maarten-pennings/P2000-cartridge/case/label-ErixCollectables-black.png

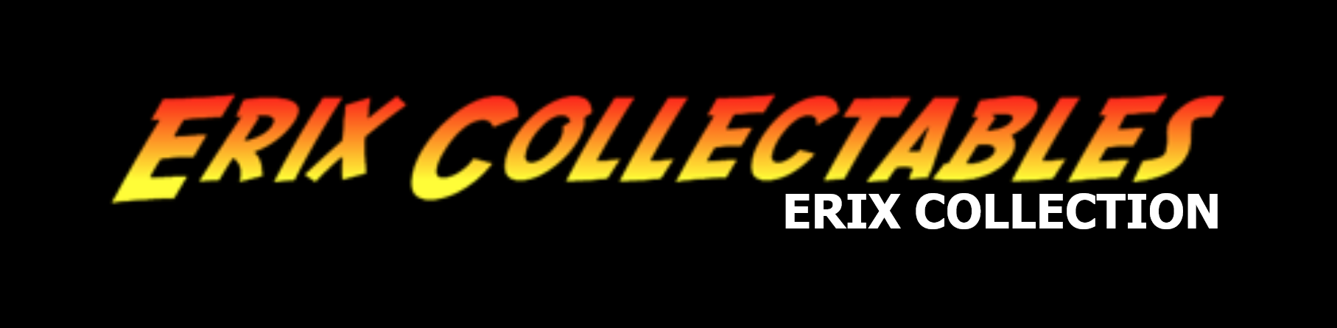
case/label-ErixCollectables-black.png
