maarten-pennings/P2000-cartridge/case/label-ErixCollectables-white.png

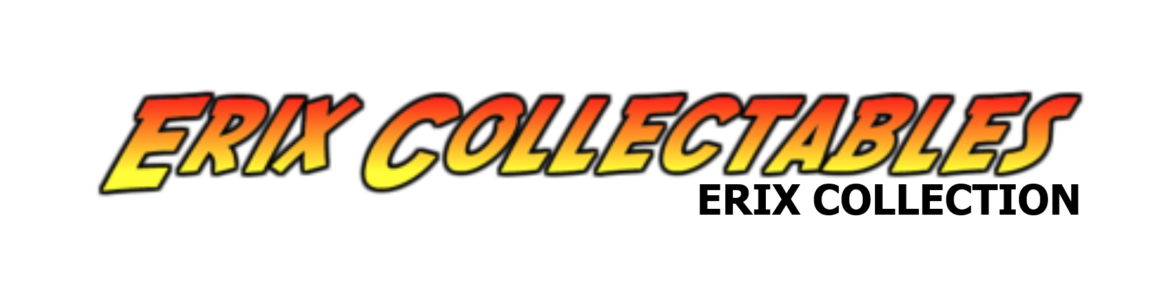
case/label-ErixCollectables-white.png
