maarten-pennings/P2000-cartridge/images/cartridge.jpg

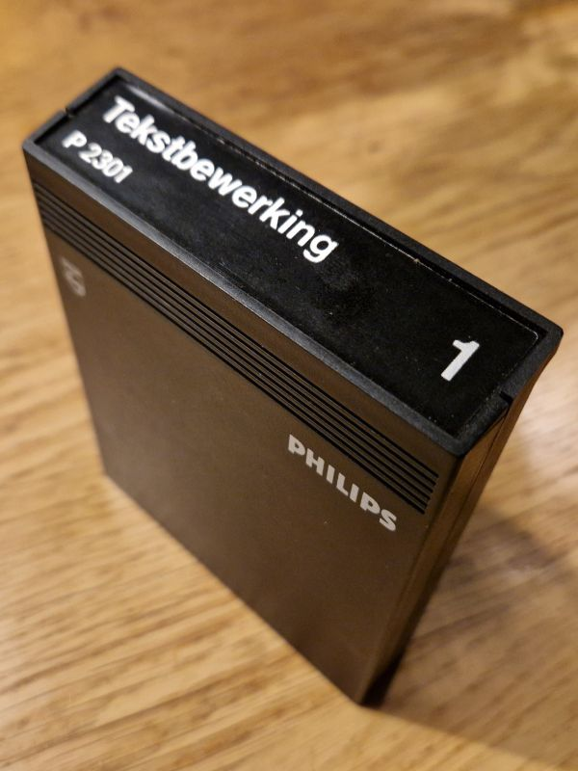
images/cartridge.jpg
