maarten-pennings/P2000-cartridge/images/invoice3Dprint.png

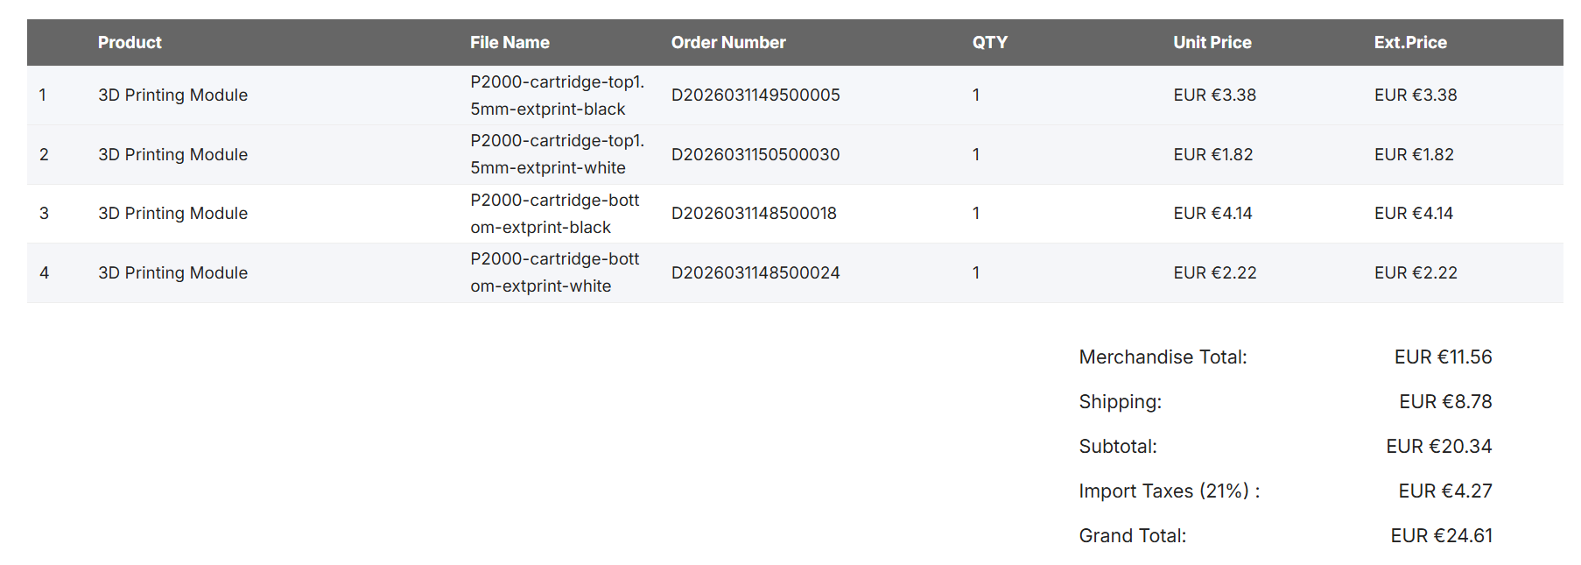
images/invoice3Dprint.png
