maarten-pennings/P2000-cartridge/images/invoice-aliexpress.png

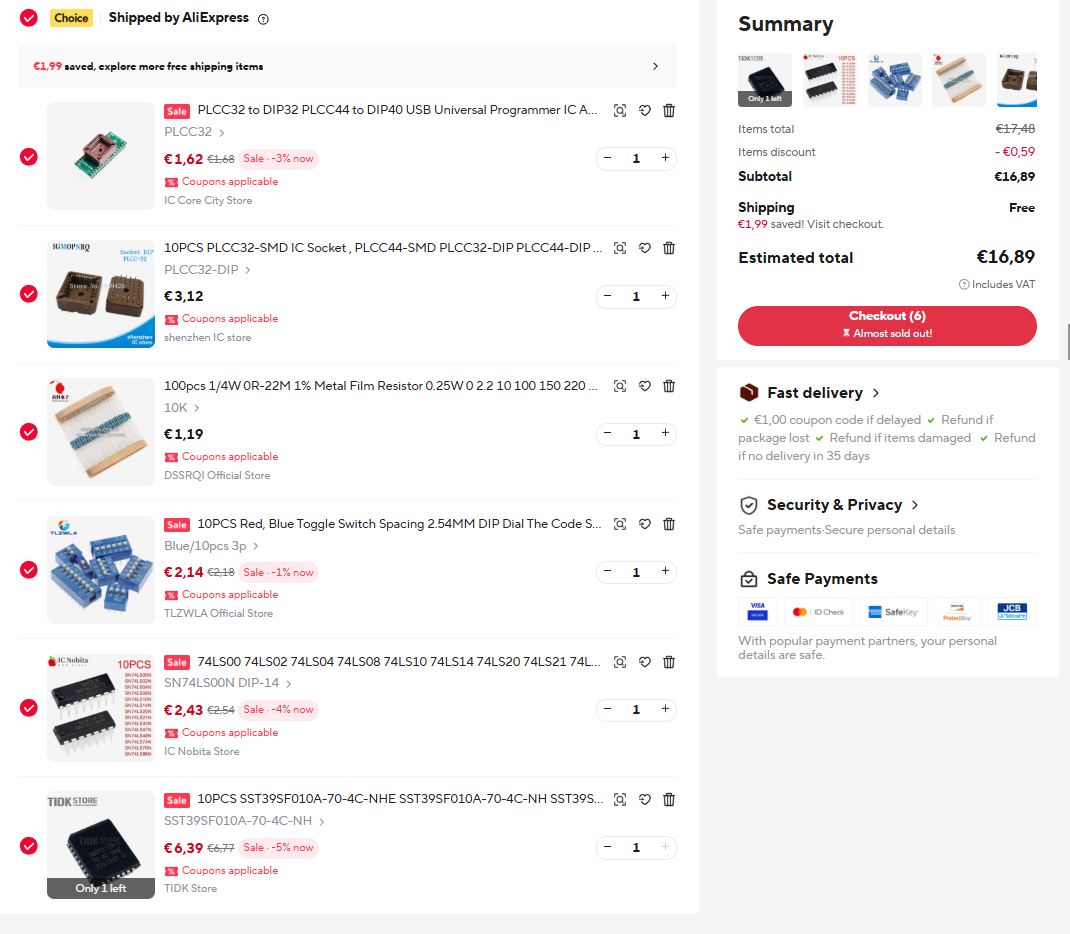
images/invoice-aliexpress.png
