maarten-pennings/P2000-cartridge/images/invoice-jlcpcb.png

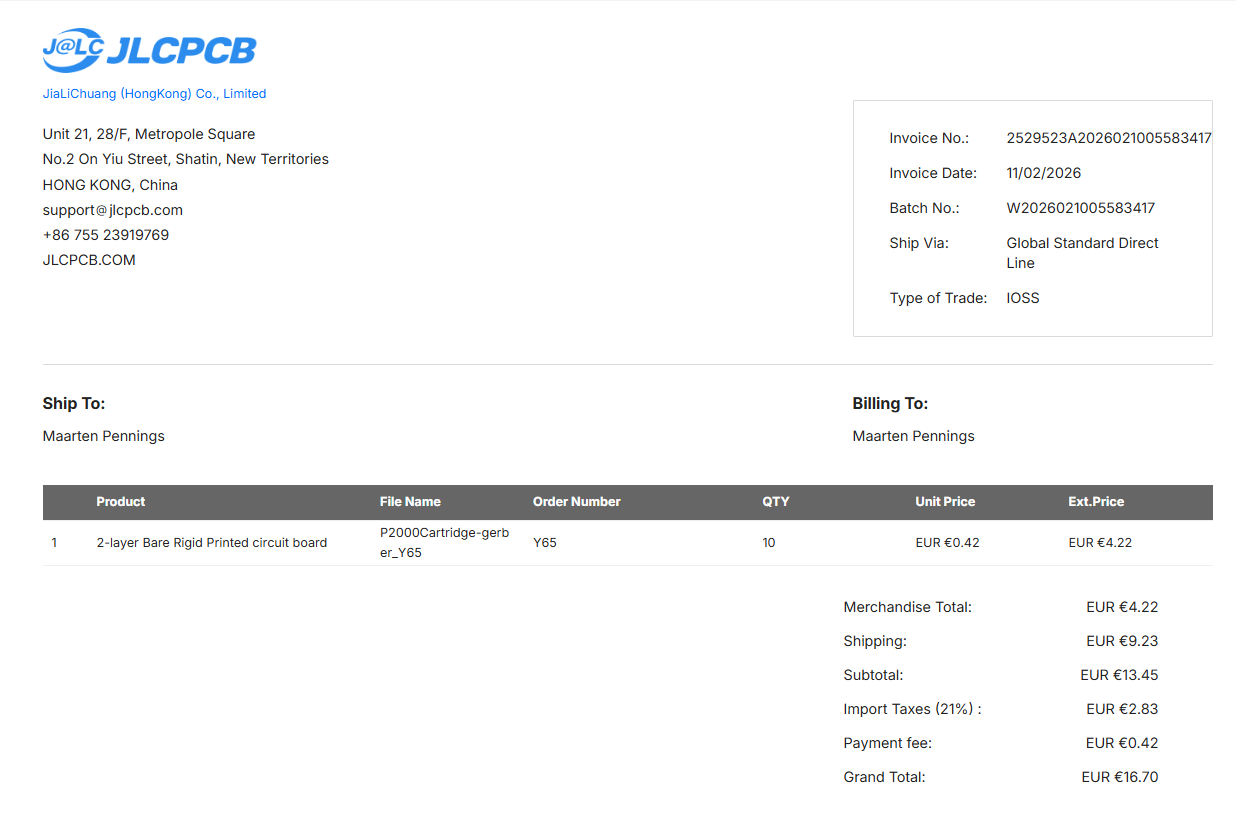
images/invoice-jlcpcb.png
