maarten-pennings/P2000-cartridge/images/pcb-on-p2000.jpg

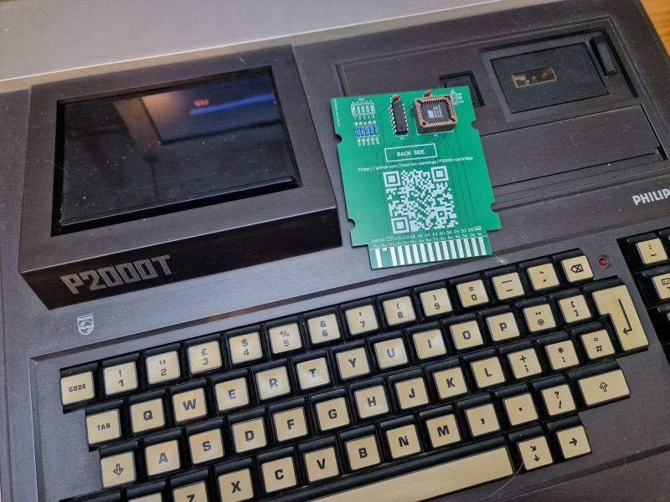
images/pcb-on-p2000.jpg
