maarten-pennings/P2000-cartridge/images/pcb-render.png

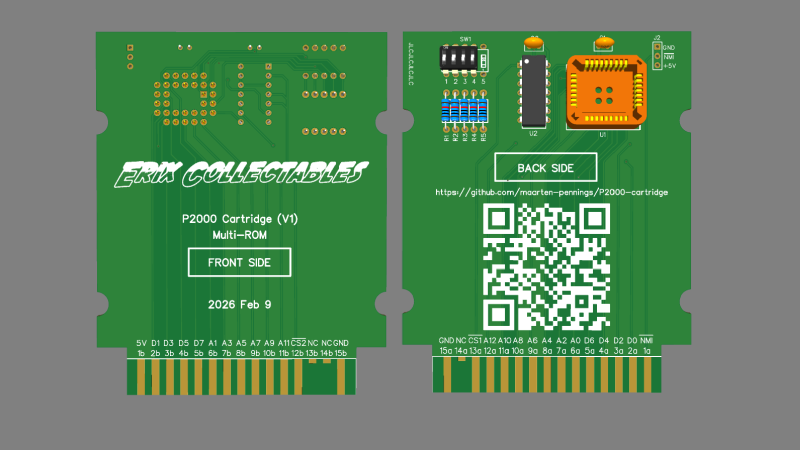
images/pcb-render.png
